StoneSet/furrtek_esl/android/src/main/java/android/support/v7/internal/widget/ScrollingTabContainerView.java

package android.support.v7.internal.widget;

import android.content.Context;
import android.content.res.Configuration;
import android.graphics.drawable.Drawable;
import android.support.v4.widget.ExploreByTouchHelper;
import android.support.v7.app.ActionBar.Tab;
import android.support.v7.appcompat.R;
import android.support.v7.internal.view.ActionBarPolicy;
import android.support.v7.internal.widget.AdapterViewICS.OnItemClickListener;
import android.text.TextUtils.TruncateAt;
import android.util.AttributeSet;
import android.view.LayoutInflater;
import android.view.View;
import android.view.View.MeasureSpec;
import android.view.View.OnClickListener;
import android.view.ViewGroup;
import android.view.ViewGroup.LayoutParams;
import android.widget.AbsListView;
import android.widget.BaseAdapter;
import android.widget.HorizontalScrollView;
import android.widget.ImageView;
import android.widget.LinearLayout;
import android.widget.TextView;

public class ScrollingTabContainerView extends HorizontalScrollView implements OnItemClickListener {
    private static final String TAG = "ScrollingTabContainerView";
    private boolean mAllowCollapse;
    private int mContentHeight;
    private final LayoutInflater mInflater;
    int mMaxTabWidth;
    private int mSelectedTabIndex;
    int mStackedTabMaxWidth;
    private TabClickListener mTabClickListener;
    private LinearLayout mTabLayout = ((LinearLayout) this.mInflater.inflate(R.layout.abc_action_bar_tabbar, this, false));
    Runnable mTabSelector;
    private SpinnerICS mTabSpinner;

    private class TabAdapter extends BaseAdapter {
        private TabAdapter() {
        }

        public int getCount() {
            return ScrollingTabContainerView.this.mTabLayout.getChildCount();
        }

        public Object getItem(int i) {
            return ((TabView) ScrollingTabContainerView.this.mTabLayout.getChildAt(i)).getTab();
        }

        public long getItemId(int i) {
            return (long) i;
        }

        public View getView(int i, View view, ViewGroup viewGroup) {
            if (view == null) {
                return ScrollingTabContainerView.this.createTabView((Tab) getItem(i), true);
            }
            ((TabView) view).bindTab((Tab) getItem(i));
            return view;
        }
    }

    private class TabClickListener implements OnClickListener {
        private TabClickListener() {
        }

        public void onClick(View view) {
            ((TabView) view).getTab().select();
            int childCount = ScrollingTabContainerView.this.mTabLayout.getChildCount();
            for (int i = 0; i < childCount; i++) {
                View childAt = ScrollingTabContainerView.this.mTabLayout.getChildAt(i);
                childAt.setSelected(childAt == view);
            }
        }
    }

    public static class TabView extends LinearLayout {
        private View mCustomView;
        private ImageView mIconView;
        private ScrollingTabContainerView mParent;
        private Tab mTab;
        private TextView mTextView;

        public TabView(Context context, AttributeSet attributeSet) {
            super(context, attributeSet);
        }

        void attach(ScrollingTabContainerView scrollingTabContainerView, Tab tab, boolean z) {
            this.mParent = scrollingTabContainerView;
            this.mTab = tab;
            if (z) {
                setGravity(19);
            }
            update();
        }

        public void bindTab(Tab tab) {
            this.mTab = tab;
            update();
        }

        public Tab getTab() {
            return this.mTab;
        }

        public void onMeasure(int i, int i2) {
            super.onMeasure(i, i2);
            int i3 = this.mParent != null ? this.mParent.mMaxTabWidth : 0;
            if (i3 > 0 && getMeasuredWidth() > i3) {
                super.onMeasure(MeasureSpec.makeMeasureSpec(i3, 1073741824), i2);
            }
        }

        public void update() {
            Tab tab = this.mTab;
            View customView = tab.getCustomView();
            if (customView != null) {
                TabView parent = customView.getParent();
                if (parent != this) {
                    if (parent != null) {
                        parent.removeView(customView);
                    }
                    addView(customView);
                }
                this.mCustomView = customView;
                if (this.mTextView != null) {
                    this.mTextView.setVisibility(8);
                }
                if (this.mIconView != null) {
                    this.mIconView.setVisibility(8);
                    this.mIconView.setImageDrawable(null);
                    return;
                }
                return;
            }
            if (this.mCustomView != null) {
                removeView(this.mCustomView);
                this.mCustomView = null;
            }
            Drawable icon = tab.getIcon();
            CharSequence text = tab.getText();
            if (icon != null) {
                if (this.mIconView == null) {
                    View imageView = new ImageView(getContext());
                    LayoutParams layoutParams = new LinearLayout.LayoutParams(-2, -2);
                    layoutParams.gravity = 16;
                    imageView.setLayoutParams(layoutParams);
                    addView(imageView, 0);
                    this.mIconView = imageView;
                }
                this.mIconView.setImageDrawable(icon);
                this.mIconView.setVisibility(0);
            } else if (this.mIconView != null) {
                this.mIconView.setVisibility(8);
                this.mIconView.setImageDrawable(null);
            }
            if (text != null) {
                if (this.mTextView == null) {
                    customView = new CompatTextView(getContext(), null, R.attr.actionBarTabTextStyle);
                    customView.setEllipsize(TruncateAt.END);
                    LayoutParams layoutParams2 = new LinearLayout.LayoutParams(-2, -2);
                    layoutParams2.gravity = 16;
                    customView.setLayoutParams(layoutParams2);
                    addView(customView);
                    this.mTextView = customView;
                }
                this.mTextView.setText(text);
                this.mTextView.setVisibility(0);
            } else if (this.mTextView != null) {
                this.mTextView.setVisibility(8);
                this.mTextView.setText(null);
            }
            if (this.mIconView != null) {
                this.mIconView.setContentDescription(tab.getContentDescription());
            }
        }
    }

    public ScrollingTabContainerView(Context context) {
        super(context);
        this.mInflater = LayoutInflater.from(context);
        setHorizontalScrollBarEnabled(false);
        ActionBarPolicy actionBarPolicy = ActionBarPolicy.get(context);
        setContentHeight(actionBarPolicy.getTabContainerHeight());
        this.mStackedTabMaxWidth = actionBarPolicy.getStackedTabMaxWidth();
        addView(this.mTabLayout, new LayoutParams(-2, -1));
    }

    private SpinnerICS createSpinner() {
        SpinnerICS spinnerICS = new SpinnerICS(getContext(), null, R.attr.actionDropDownStyle);
        spinnerICS.setLayoutParams(new LinearLayout.LayoutParams(-2, -1));
        spinnerICS.setOnItemClickListenerInt(this);
        return spinnerICS;
    }

    private TabView createTabView(Tab tab, boolean z) {
        TabView tabView = (TabView) this.mInflater.inflate(R.layout.abc_action_bar_tab, this.mTabLayout, false);
        tabView.attach(this, tab, z);
        if (z) {
            tabView.setBackgroundDrawable(null);
            tabView.setLayoutParams(new AbsListView.LayoutParams(-1, this.mContentHeight));
        } else {
            tabView.setFocusable(true);
            if (this.mTabClickListener == null) {
                this.mTabClickListener = new TabClickListener();
            }
            tabView.setOnClickListener(this.mTabClickListener);
        }
        return tabView;
    }

    private boolean isCollapsed() {
        return this.mTabSpinner != null && this.mTabSpinner.getParent() == this;
    }

    private void performCollapse() {
        if (!isCollapsed()) {
            if (this.mTabSpinner == null) {
                this.mTabSpinner = createSpinner();
            }
            removeView(this.mTabLayout);
            addView(this.mTabSpinner, new LayoutParams(-2, -1));
            if (this.mTabSpinner.getAdapter() == null) {
                this.mTabSpinner.setAdapter(new TabAdapter());
            }
            if (this.mTabSelector != null) {
                removeCallbacks(this.mTabSelector);
                this.mTabSelector = null;
            }
            this.mTabSpinner.setSelection(this.mSelectedTabIndex);
        }
    }

    private boolean performExpand() {
        if (isCollapsed()) {
            removeView(this.mTabSpinner);
            addView(this.mTabLayout, new LayoutParams(-2, -1));
            setTabSelected(this.mTabSpinner.getSelectedItemPosition());
        }
        return false;
    }

    public void addTab(Tab tab, int i, boolean z) {
        View createTabView = createTabView(tab, false);
        this.mTabLayout.addView(createTabView, i, new LinearLayout.LayoutParams(0, -1, 1.0f));
        if (this.mTabSpinner != null) {
            ((TabAdapter) this.mTabSpinner.getAdapter()).notifyDataSetChanged();
        }
        if (z) {
            createTabView.setSelected(true);
        }
        if (this.mAllowCollapse) {
            requestLayout();
        }
    }

    public void addTab(Tab tab, boolean z) {
        View createTabView = createTabView(tab, false);
        this.mTabLayout.addView(createTabView, new LinearLayout.LayoutParams(0, -1, 1.0f));
        if (this.mTabSpinner != null) {
            ((TabAdapter) this.mTabSpinner.getAdapter()).notifyDataSetChanged();
        }
        if (z) {
            createTabView.setSelected(true);
        }
        if (this.mAllowCollapse) {
            requestLayout();
        }
    }

    public void animateToTab(int i) {
        final View childAt = this.mTabLayout.getChildAt(i);
        if (this.mTabSelector != null) {
            removeCallbacks(this.mTabSelector);
        }
        this.mTabSelector = new Runnable() {
            public void run() {
                ScrollingTabContainerView.this.smoothScrollTo(childAt.getLeft() - ((ScrollingTabContainerView.this.getWidth() - childAt.getWidth()) / 2), 0);
                ScrollingTabContainerView.this.mTabSelector = null;
            }
        };
        post(this.mTabSelector);
    }

    public void onAttachedToWindow() {
        super.onAttachedToWindow();
        if (this.mTabSelector != null) {
            post(this.mTabSelector);
        }
    }

    protected void onConfigurationChanged(Configuration configuration) {
        ActionBarPolicy actionBarPolicy = ActionBarPolicy.get(getContext());
        setContentHeight(actionBarPolicy.getTabContainerHeight());
        this.mStackedTabMaxWidth = actionBarPolicy.getStackedTabMaxWidth();
    }

    public void onDetachedFromWindow() {
        super.onDetachedFromWindow();
        if (this.mTabSelector != null) {
            removeCallbacks(this.mTabSelector);
        }
    }

    public void onItemClick(AdapterViewICS<?> adapterViewICS, View view, int i, long j) {
        ((TabView) view).getTab().select();
    }

    public void onMeasure(int i, int i2) {
        int i3 = 1;
        int mode = MeasureSpec.getMode(i);
        boolean z = mode == 1073741824;
        setFillViewport(z);
        int childCount = this.mTabLayout.getChildCount();
        if (childCount <= 1 || !(mode == 1073741824 || mode == ExploreByTouchHelper.INVALID_ID)) {
            this.mMaxTabWidth = -1;
        } else {
            if (childCount > 2) {
                this.mMaxTabWidth = (int) (0.4f * ((float) MeasureSpec.getSize(i)));
            } else {
                this.mMaxTabWidth = MeasureSpec.getSize(i) / 2;
            }
            this.mMaxTabWidth = Math.min(this.mMaxTabWidth, this.mStackedTabMaxWidth);
        }
        mode = MeasureSpec.makeMeasureSpec(this.mContentHeight, 1073741824);
        if (z || !this.mAllowCollapse) {
            i3 = 0;
        }
        if (i3 != 0) {
            this.mTabLayout.measure(0, mode);
            if (this.mTabLayout.getMeasuredWidth() > MeasureSpec.getSize(i)) {
                performCollapse();
            } else {
                performExpand();
            }
        } else {
            performExpand();
        }
        i3 = getMeasuredWidth();
        super.onMeasure(i, mode);
        int measuredWidth = getMeasuredWidth();
        if (z && i3 != measuredWidth) {
            setTabSelected(this.mSelectedTabIndex);
        }
    }

    public void removeAllTabs() {
        this.mTabLayout.removeAllViews();
        if (this.mTabSpinner != null) {
            ((TabAdapter) this.mTabSpinner.getAdapter()).notifyDataSetChanged();
        }
        if (this.mAllowCollapse) {
            requestLayout();
        }
    }

    public void removeTabAt(int i) {
        this.mTabLayout.removeViewAt(i);
        if (this.mTabSpinner != null) {
            ((TabAdapter) this.mTabSpinner.getAdapter()).notifyDataSetChanged();
        }
        if (this.mAllowCollapse) {
            requestLayout();
        }
    }

    public void setAllowCollapse(boolean z) {
        this.mAllowCollapse = z;
    }

    public void setContentHeight(int i) {
        this.mContentHeight = i;
        requestLayout();
    }

    public void setTabSelected(int i) {
        this.mSelectedTabIndex = i;
        int childCount = this.mTabLayout.getChildCount();
        int i2 = 0;
        while (i2 < childCount) {
            View childAt = this.mTabLayout.getChildAt(i2);
            boolean z = i2 == i;
            childAt.setSelected(z);
            if (z) {
                animateToTab(i);
            }
            i2++;
        }
        if (this.mTabSpinner != null && i >= 0) {
            this.mTabSpinner.setSelection(i);
        }
    }

    public void updateTab(int i) {
        ((TabView) this.mTabLayout.getChildAt(i)).update();
        if (this.mTabSpinner != null) {
            ((TabAdapter) this.mTabSpinner.getAdapter()).notifyDataSetChanged();
        }
        if (this.mAllowCollapse) {
            requestLayout();
        }
    }
}
